daviddoo02/Legolas-an-open-source-biped/CAD/Servo and electronics/40 kg Servo.SLDPRT

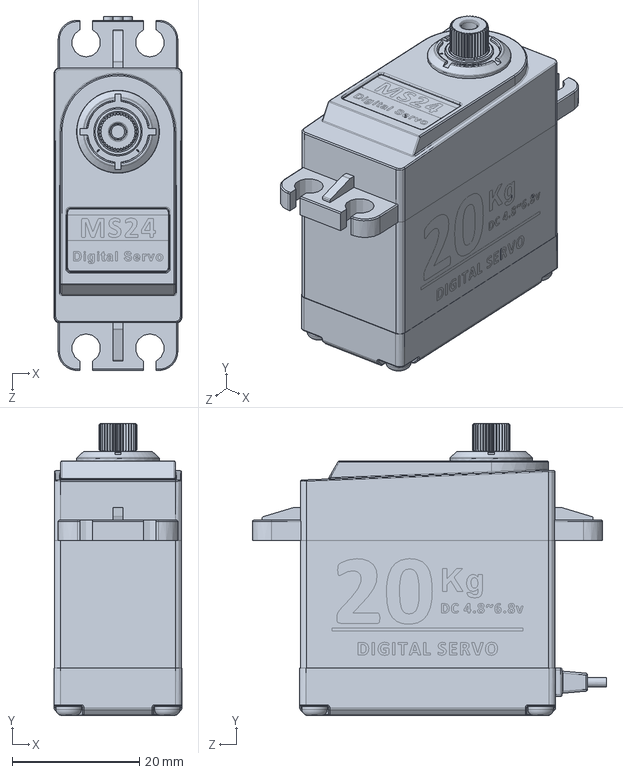
[picture p19: CAD file, 2024-01-15]
CAD/Servo and electronics/40 kg Servo.SLDPRT
20.1 x 45.9 x 55.6 mm
