daviddoo02/Legolas-an-open-source-biped/Mujoco xml/References/agility_cassie/assets/hip-roll.obj

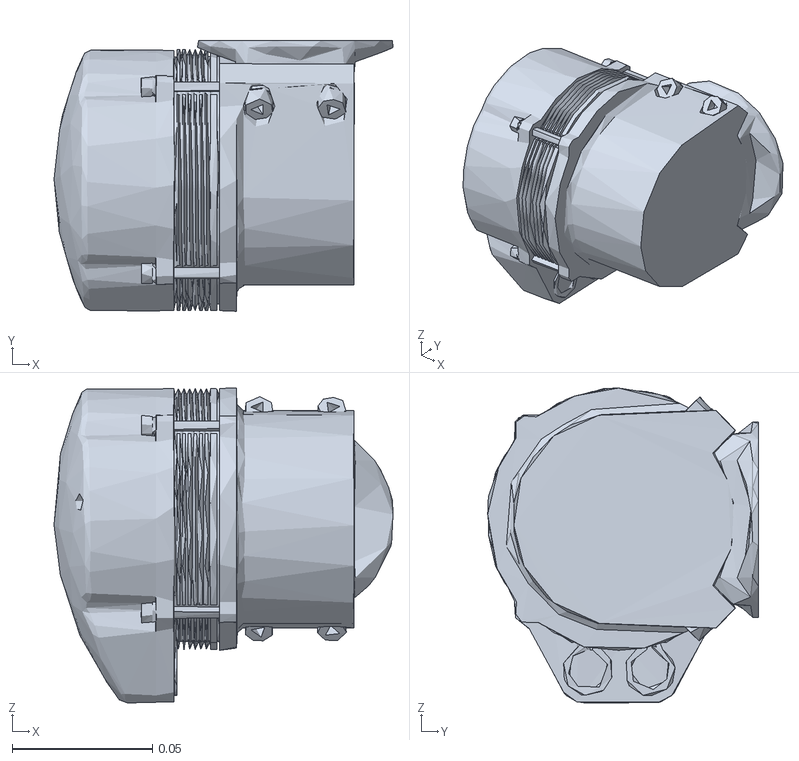
[picture p20: CAD file, 2023-01-17]
Mujoco xml/References/agility_cassie/assets/hip-roll.obj
0.121 x 0.0964 x 0.112
