daviddoo02/Legolas-an-open-source-biped/Working Mk 5/meshes/R_Servo.STL

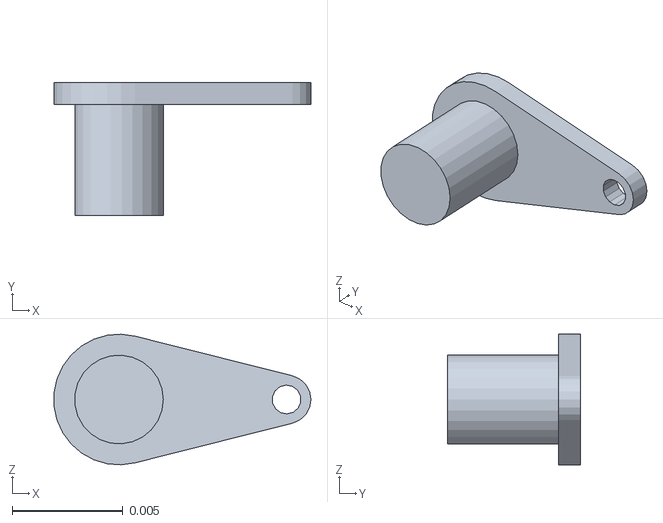
[picture p21: CAD file, 2023-01-25]
Working Mk 5/meshes/R_Servo.STL
0.0116 x 0.006 x 0.00589
