daviddoo02/Legolas-an-open-source-biped/CAD/Servo and electronics/80kg_servo_arm.SLDPRT

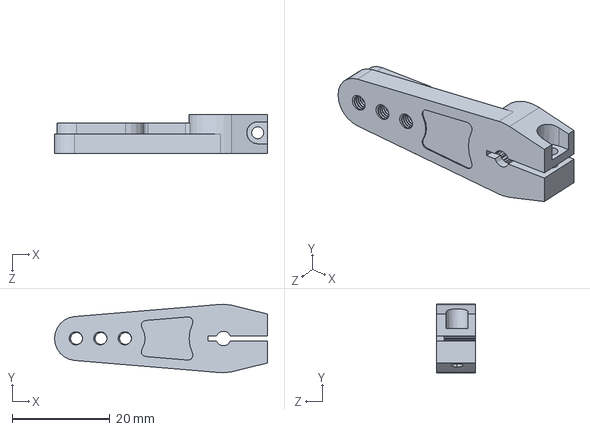
[picture p22: CAD file, 2024-01-15]
CAD/Servo and electronics/80kg_servo_arm.SLDPRT
43.5 x 14.0 x 8.00 mm
