daviddoo02/Legolas-an-open-source-biped/Mujoco xml/References/agility_cassie/assets/tarsus.obj

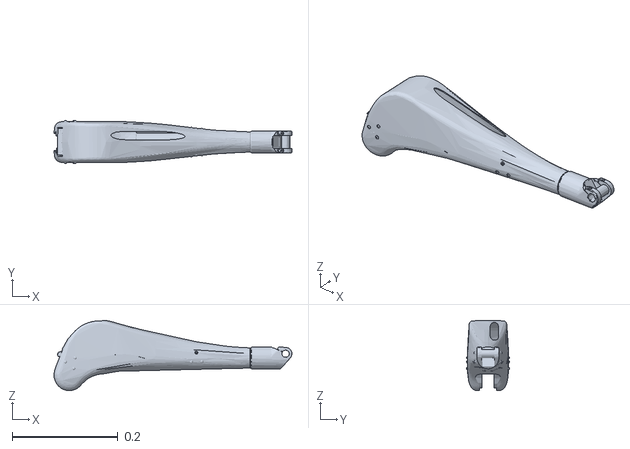
[picture p23: CAD file, 2023-01-17]
Mujoco xml/References/agility_cassie/assets/tarsus.obj
0.449 x 0.0807 x 0.132
