daviddoo02/Legolas-an-open-source-biped/Working Mk 5/meshes/R_Shin.STL

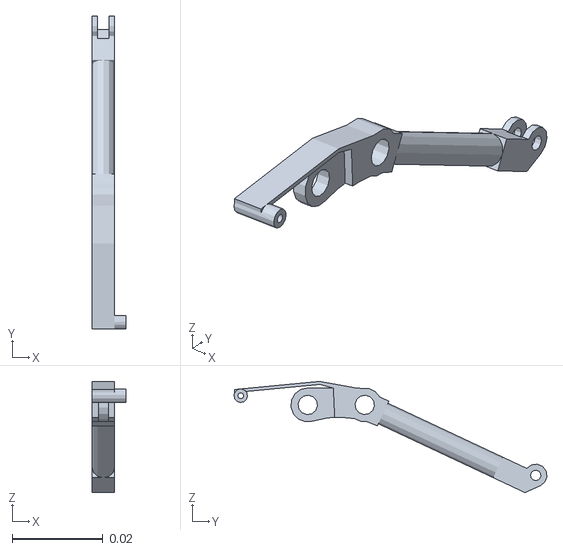
[picture p24: CAD file, 2023-01-25]
Working Mk 5/meshes/R_Shin.STL
0.0075 x 0.0691 x 0.0246
