daviddoo02/Legolas-an-open-source-biped/Mujoco xml/References/agility_cassie/assets/foot-crank.obj

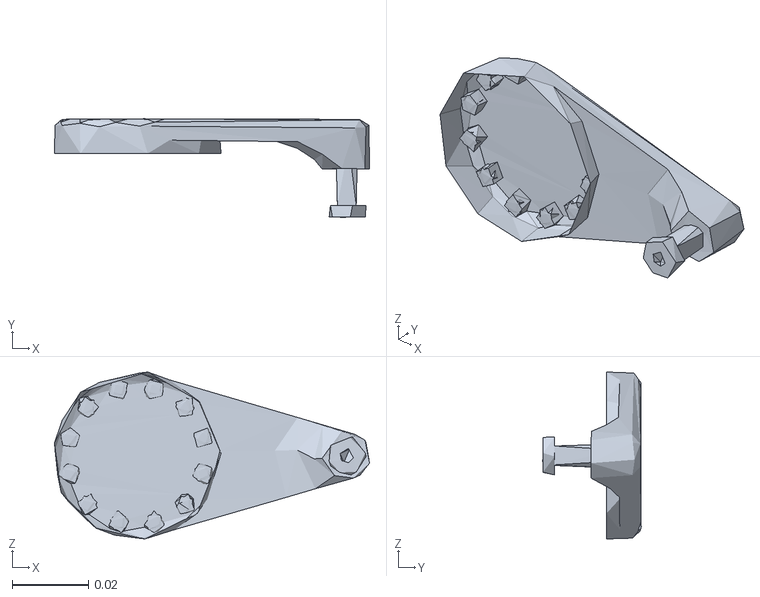
[picture p25: CAD file, 2023-01-17]
Mujoco xml/References/agility_cassie/assets/foot-crank.obj
0.0824 x 0.0258 x 0.0437
