daviddoo02/Legolas-an-open-source-biped/Working Mk 5/meshes/R_Linkage.STL

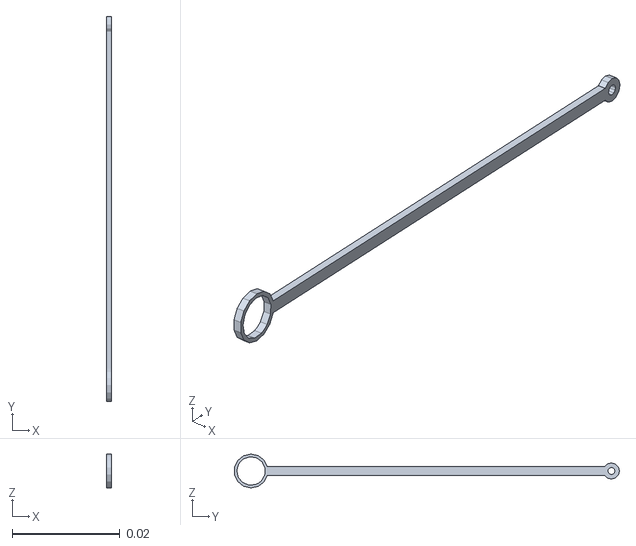
[picture p26: CAD file, 2023-01-25]
Working Mk 5/meshes/R_Linkage.STL
0.001 x 0.0715 x 0.0063
