daviddoo02/Legolas-an-open-source-biped/CAD/Servo and electronics/80kg_servo.SLDPRT

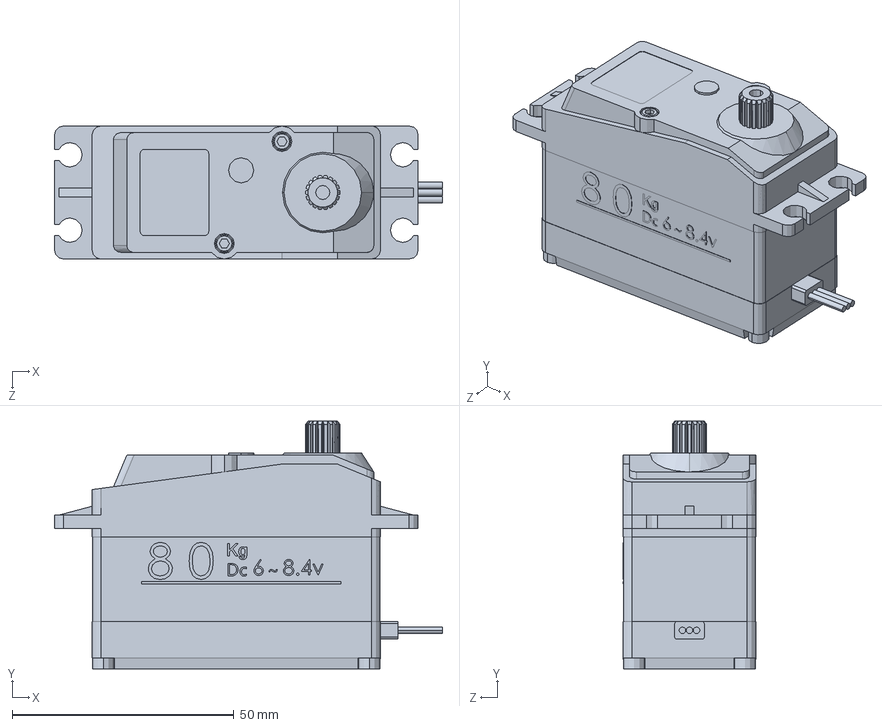
[picture p27: CAD file, 2024-01-15]
CAD/Servo and electronics/80kg_servo.SLDPRT
87.5 x 55.9 x 30.0 mm
