daviddoo02/Legolas-an-open-source-biped/Mujoco xml/References/agility_cassie/assets/shin.obj

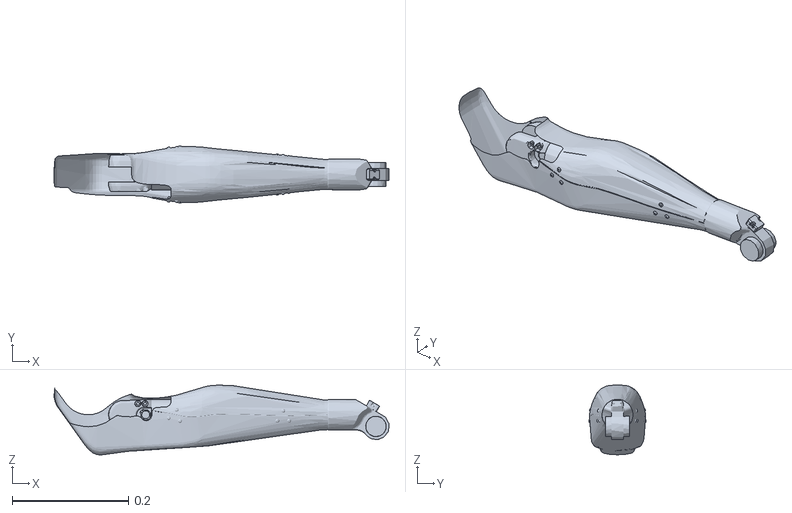
[picture p28: CAD file, 2023-01-17]
Mujoco xml/References/agility_cassie/assets/shin.obj
0.576 x 0.0987 x 0.12
