daviddoo02/Legolas-an-open-source-biped/Working Mk 5/meshes/R_Servo_Link.STL

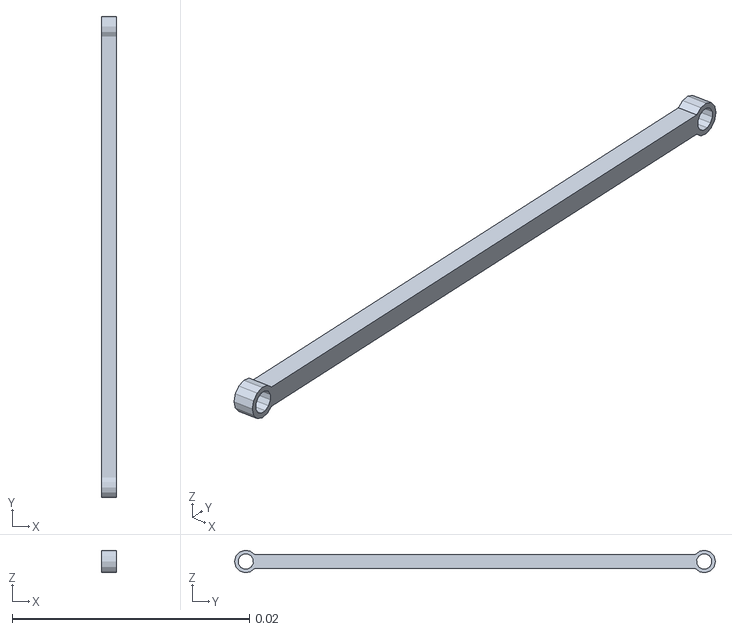
[picture p29: CAD file, 2023-01-25]
Working Mk 5/meshes/R_Servo_Link.STL
0.00125 x 0.0405 x 0.00189
