daviddoo02/Legolas-an-open-source-biped/CAD/Servo and electronics/40 kg Servo Arm.SLDPRT

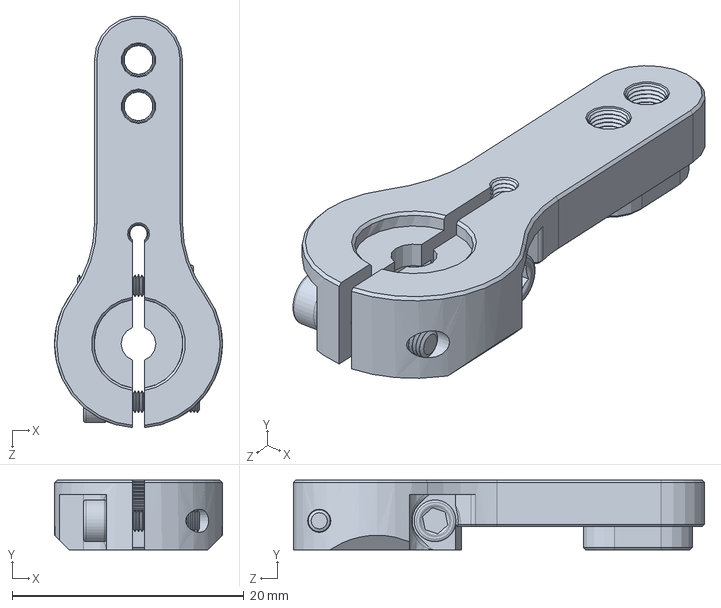
[picture p30: CAD file, 2024-01-15]
CAD/Servo and electronics/40 kg Servo Arm.SLDPRT
14.5 x 6.00 x 35.5 mm
