daviddoo02/Legolas-an-open-source-biped/Mujoco xml/References/agility_cassie/assets/knee.obj

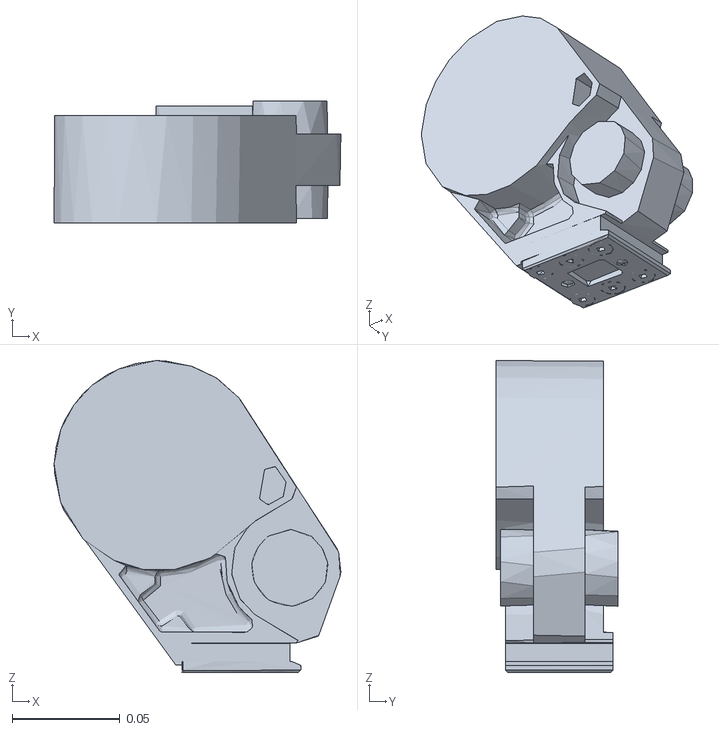
[picture p31: CAD file, 2023-01-17]
Mujoco xml/References/agility_cassie/assets/knee.obj
0.133 x 0.0568 x 0.145
