daviddoo02/Legolas-an-open-source-biped/Working Mk 5/meshes/R_Foreleg.STL

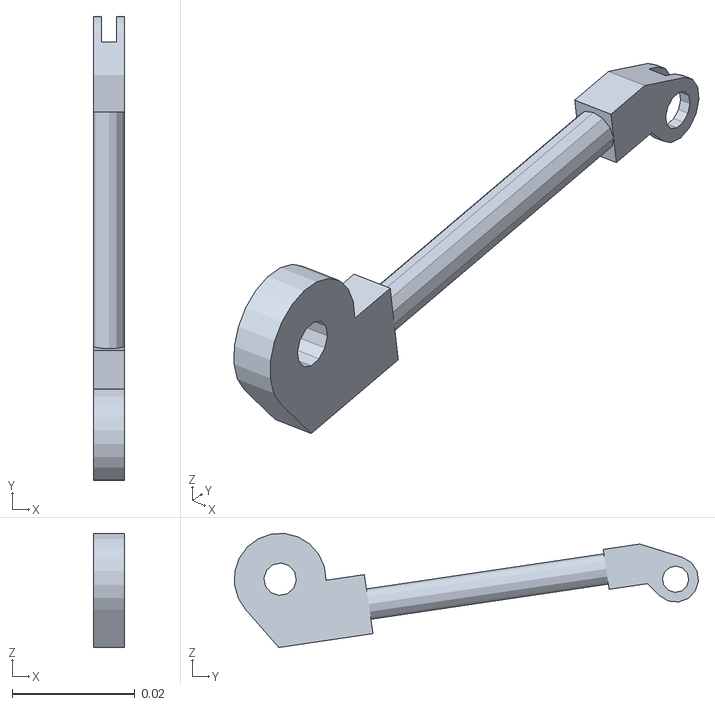
[picture p32: CAD file, 2023-01-25]
Working Mk 5/meshes/R_Foreleg.STL
0.005 x 0.0757 x 0.0186
