daviddoo02/Legolas-an-open-source-biped/Mujoco xml/References/agility_cassie/assets/knee-spring.obj

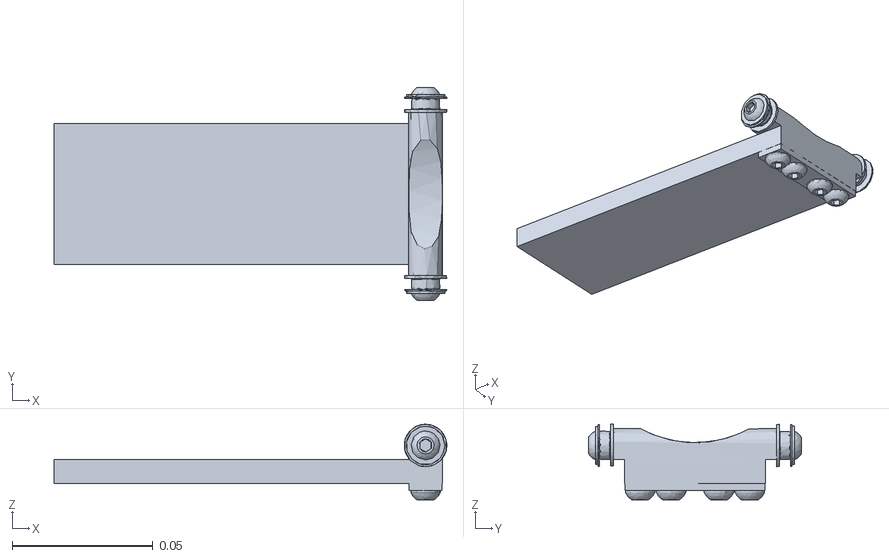
[picture p33: CAD file, 2023-01-17]
Mujoco xml/References/agility_cassie/assets/knee-spring.obj
0.14 x 0.0756 x 0.0268
