daviddoo02/Legolas-an-open-source-biped/Working Mk 5/meshes/R_Foot.STL

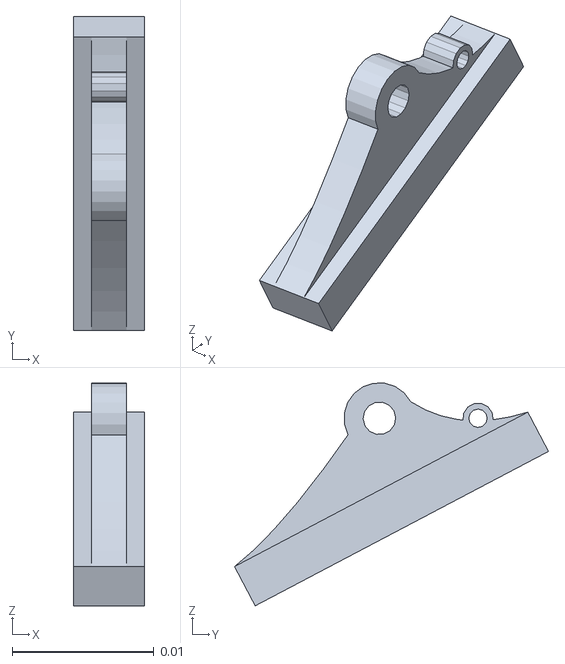
[picture p34: CAD file, 2023-01-25]
Working Mk 5/meshes/R_Foot.STL
0.005 x 0.0221 x 0.0157
