daviddoo02/Legolas-an-open-source-biped/CAD/Servo and electronics/ADS1115.SLDPRT

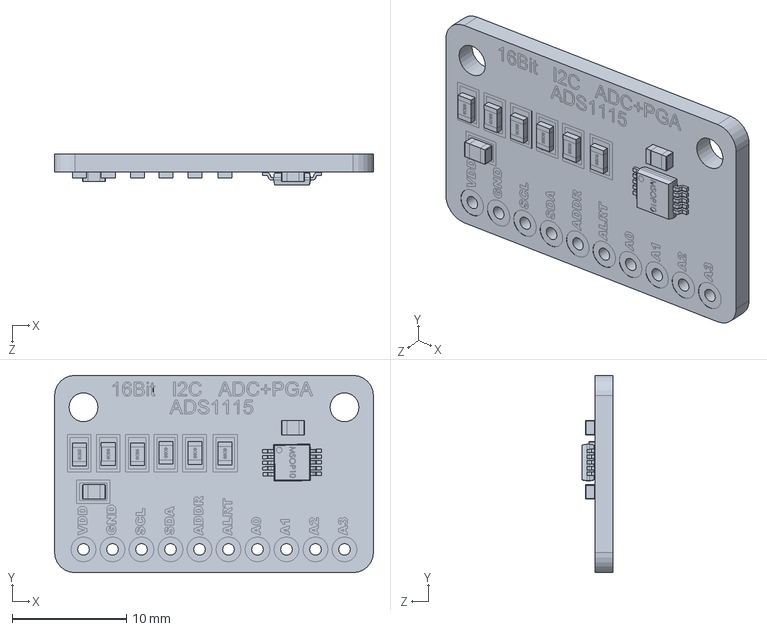
[picture p35: CAD file, 2024-01-15]
CAD/Servo and electronics/ADS1115.SLDPRT
27.9 x 17.3 x 2.74 mm
