daviddoo02/Legolas-an-open-source-biped/Mujoco xml/References/agility_cassie/assets/heel-spring.obj

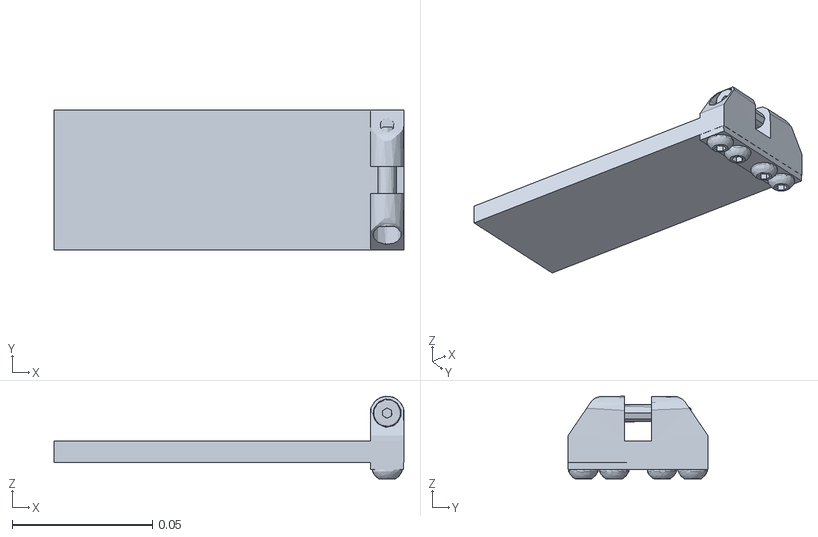
[picture p36: CAD file, 2023-01-17]
Mujoco xml/References/agility_cassie/assets/heel-spring.obj
0.125 x 0.05 x 0.0294
