daviddoo02/Legolas-an-open-source-biped/Working Mk 5/meshes/R_Thigh.STL

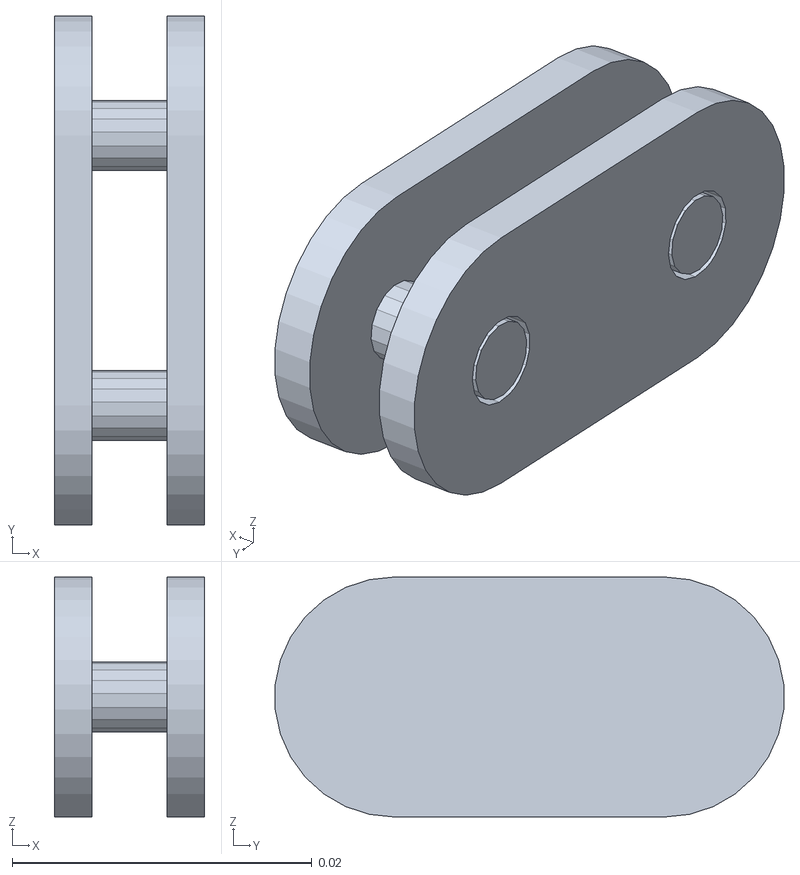
[picture p37: CAD file, 2023-01-25]
Working Mk 5/meshes/R_Thigh.STL
0.01 x 0.0339 x 0.016
