daviddoo02/Legolas-an-open-source-biped/CAD/Servo and electronics/M4 Ball Joint Rod End.SLDPRT

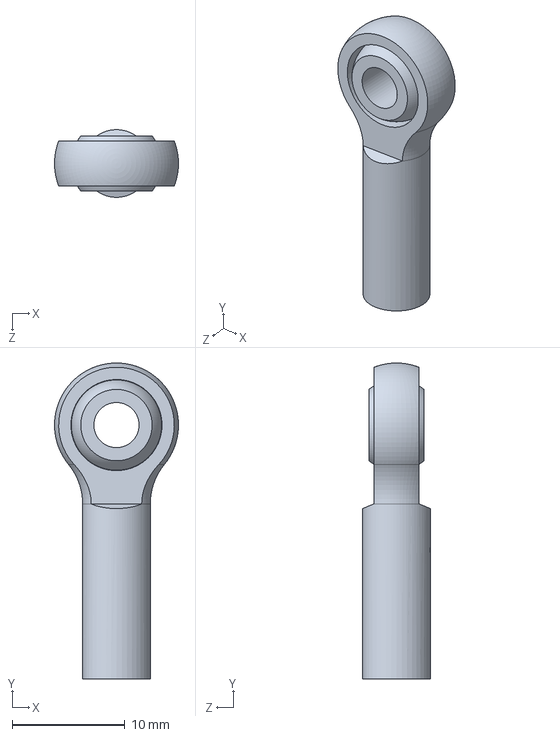
[picture p38: CAD file, 2023-05-22]
CAD/Servo and electronics/M4 Ball Joint Rod End.SLDPRT
11.0 x 28.0 x 6.00 mm
