daviddoo02/Legolas-an-open-source-biped/Mujoco xml/References/agility_cassie/assets/hip-yaw.obj

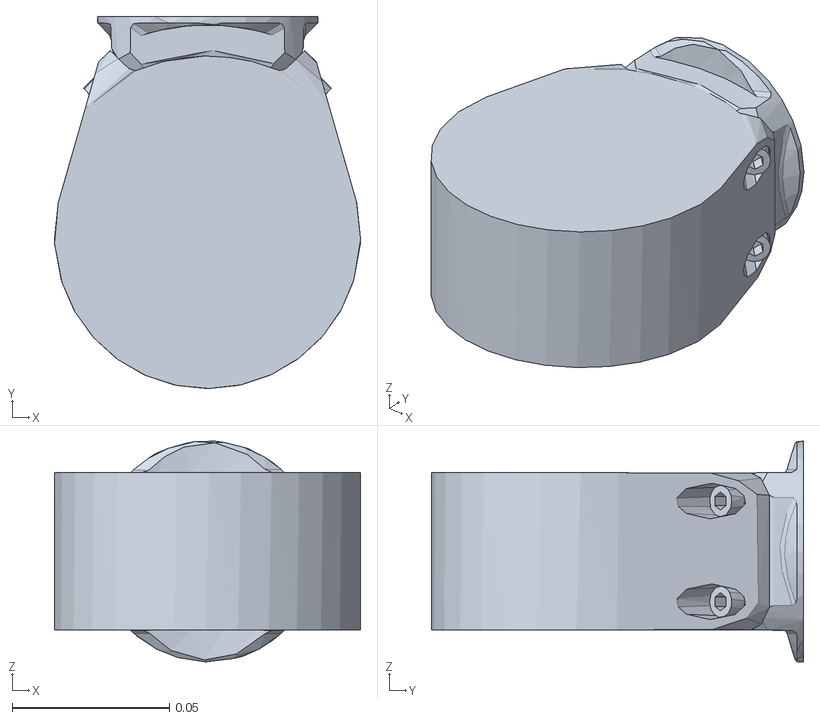
[picture p39: CAD file, 2023-01-17]
Mujoco xml/References/agility_cassie/assets/hip-yaw.obj
0.0973 x 0.118 x 0.0702
