daviddoo02/Legolas-an-open-source-biped/Working Mk 5/meshes/R_Hip_1.STL

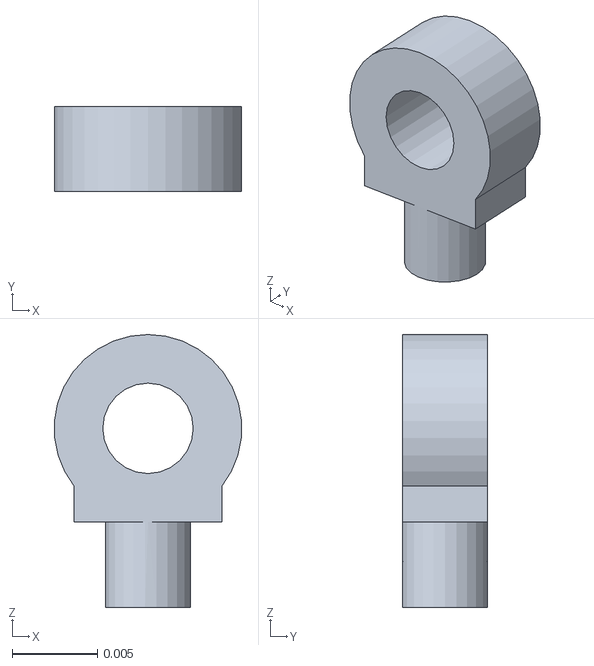
[picture p40: CAD file, 2023-01-24]
Working Mk 5/meshes/R_Hip_1.STL
0.011 x 0.005 x 0.016
