daviddoo02/Legolas-an-open-source-biped/CAD/Servo and electronics/M5 Connecting Rod.SLDPRT

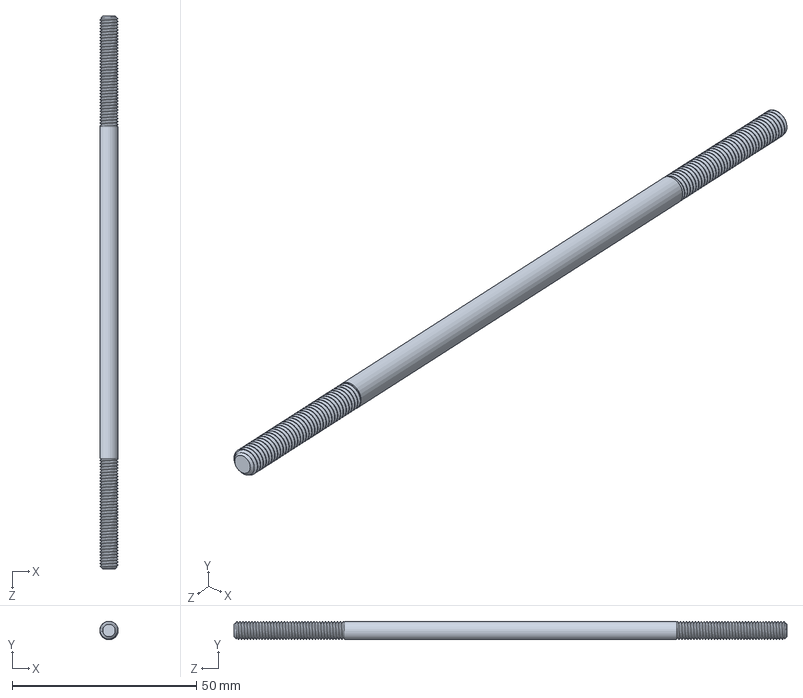
[picture p41: CAD file, 2023-05-22]
CAD/Servo and electronics/M5 Connecting Rod.SLDPRT
5.00 x 5.00 x 150.0 mm
