daviddoo02/Legolas-an-open-source-biped/Mujoco xml/References/agility_cassie/assets/foot.obj

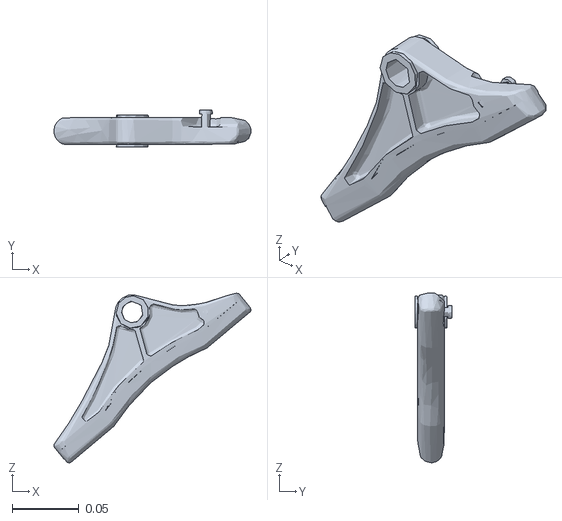
[picture p42: CAD file, 2023-01-17]
Mujoco xml/References/agility_cassie/assets/foot.obj
0.148 x 0.0277 x 0.127
