daviddoo02/Legolas-an-open-source-biped/CAD/Servo and electronics/M5 Ball Joint Rod End.SLDPRT

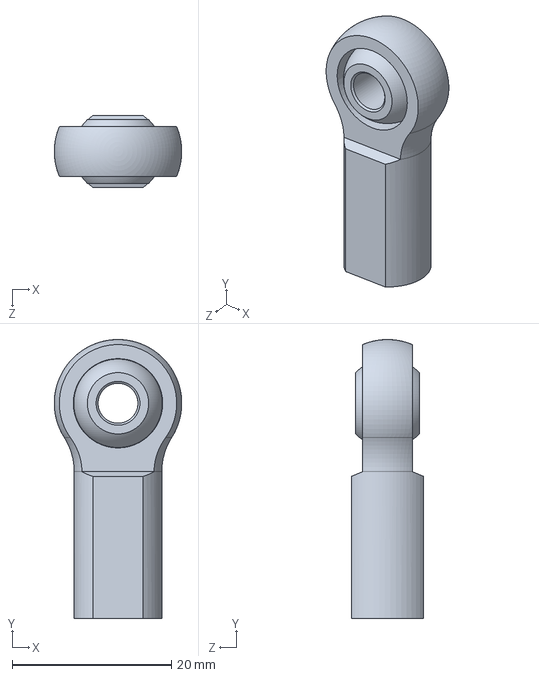
[picture p43: CAD file, 2023-05-22]
CAD/Servo and electronics/M5 Ball Joint Rod End.SLDPRT
16.0 x 35.0 x 9.00 mm
