daviddoo02/Legolas-an-open-source-biped/CAD/Servo and electronics/M4 Connecting Rod.SLDPRT

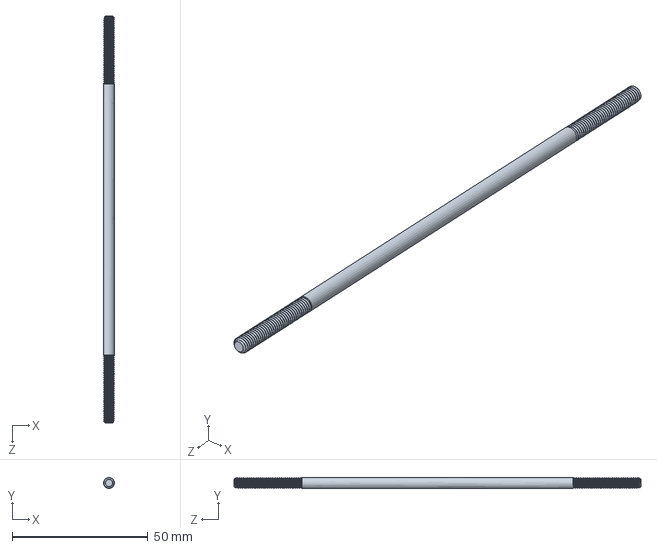
[picture p44: CAD file, 2023-05-22]
CAD/Servo and electronics/M4 Connecting Rod.SLDPRT
4.00 x 4.00 x 150.0 mm
