daviddoo02/Legolas-an-open-source-biped/Working Mk 5/meshes/L_Hip_2.STL

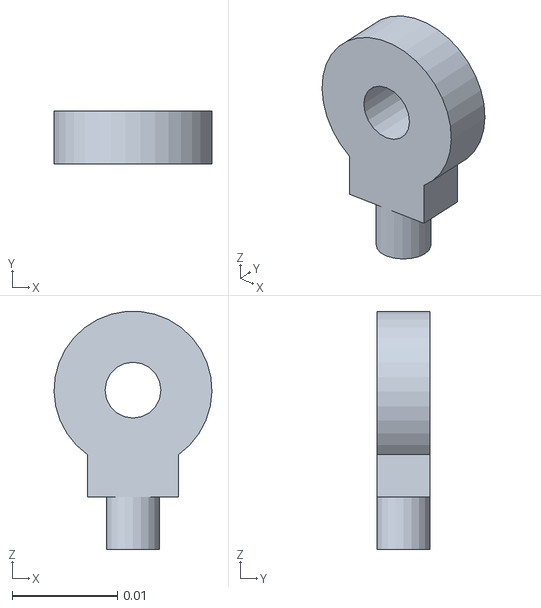
[picture p45: CAD file, 2023-01-24]
Working Mk 5/meshes/L_Hip_2.STL
0.015 x 0.005 x 0.0226
