daviddoo02/Legolas-an-open-source-biped/Working Mk 5/meshes/L_Thigh.STL

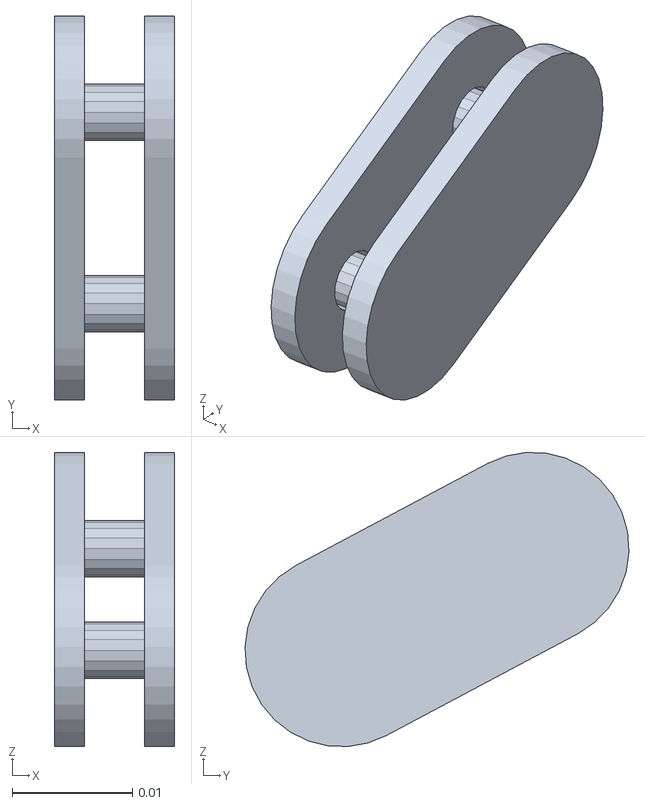
[picture p46: CAD file, 2023-01-24]
Working Mk 5/meshes/L_Thigh.STL
0.01 x 0.0319 x 0.0244
