daviddoo02/Legolas-an-open-source-biped/Working Mk 5/meshes/base_link_collision.STL

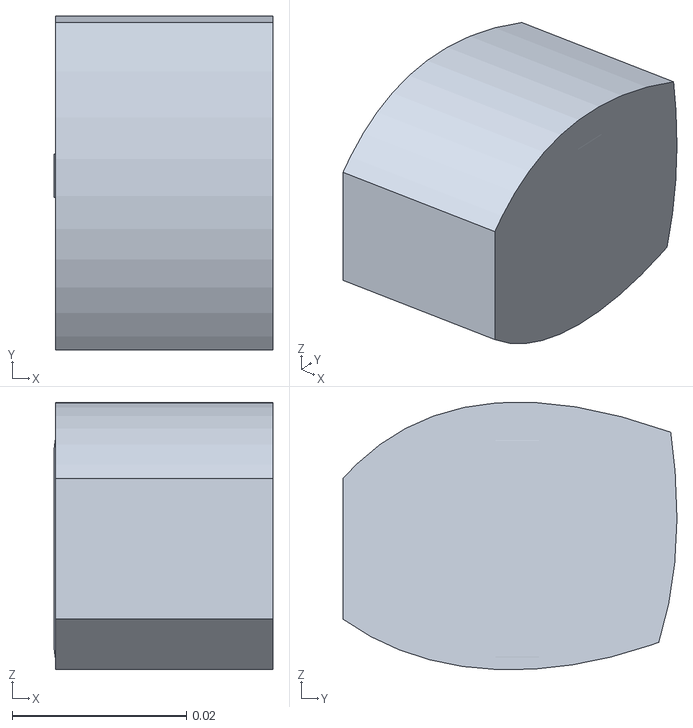
[picture p47: CAD file, 2023-01-09]
Working Mk 5/meshes/base_link_collision.STL
0.0252 x 0.0384 x 0.0307
