daviddoo02/Legolas-an-open-source-biped/Working Mk 5/meshes/base_link.STL

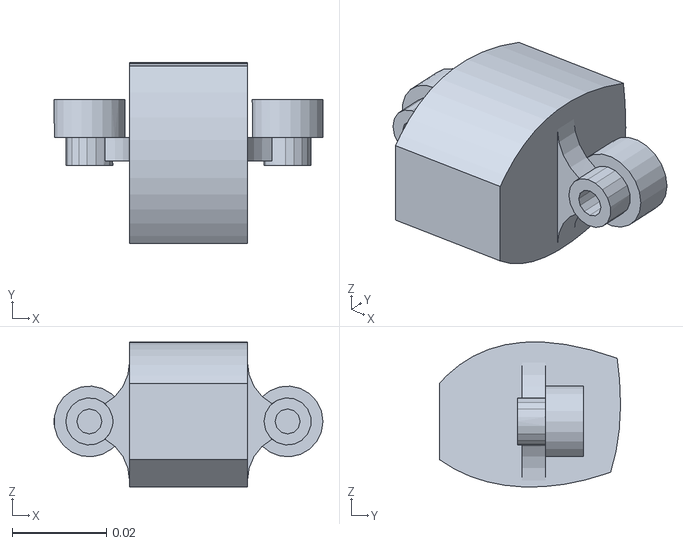
[picture p48: CAD file, 2023-01-08]
Working Mk 5/meshes/base_link.STL
0.057 x 0.0384 x 0.0307
